pc2005cz/L2_cache_adapter/adapter_SMD_bottom.png

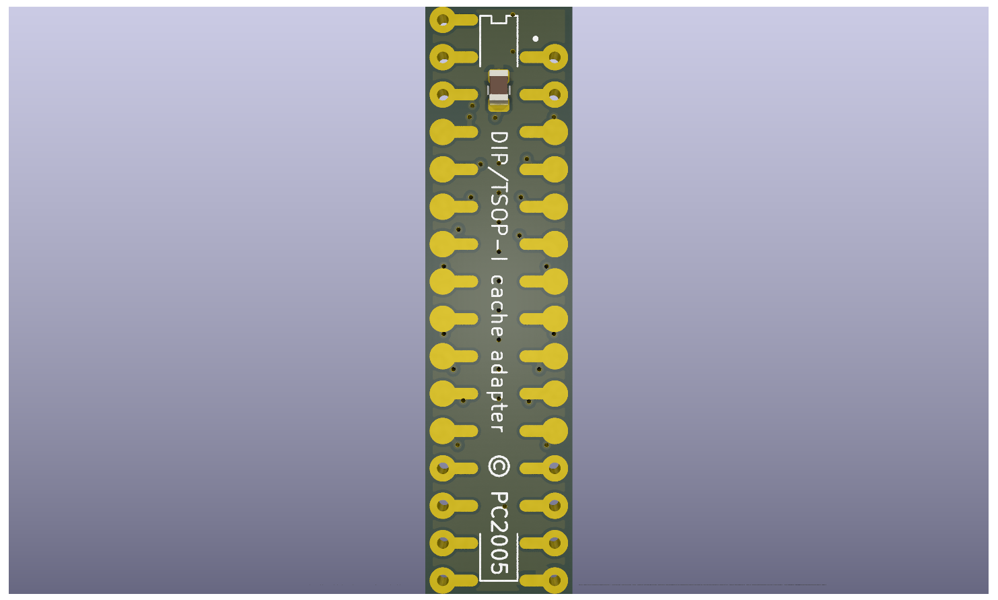
adapter_SMD_bottom.png
